adamgreig/ffp/firmware/src/hal/mod.rs

// Copyright 2019 Adam Greig
// Dual licensed under the Apache 2.0 and MIT licenses.

pub mod flash;
pub mod rcc;
pub mod nvic;
pub mod gpio;
pub mod dma;
pub mod spi;
pub mod usb;
pub mod uart;
pub mod bootload;
pub mod unique_id;
